BadenLab/poorlabs_led_driver/software/arduino/test_sketch/test_sketch.ino

const int8_t array_LED1[12][3] PROGMEM = {{0,100,0},//1
                                          {0,100,0},//2
                                          {0,100,0},//3
                                          {0,100,0},//4
                                          {0,100,0},//5
                                          {0,100,0},//6
                                          {0,100,0},//7
                                          {0,100,0},//8
                                          {0,100,0},//9
                                          {0,100,0},//10
                                          {0,100,0},//11
                                          {0,100,0},//12
};

void setup() {
  // put your setup code here, to run once:

}

void loop() {
  // put your main code here, to run repeatedly:

}
